pavan-firmware/EH-Master-Repo/docs/phase12-production-blockers.md

# EH Home — Phase 12 Production Blockers & Readiness Matrix

**Date**: 2026-08-30
**Baseline Commit**: `342425b`
**Feature Branch**: `feature/phase12-production-readiness`

---

## 1. Blocker Classification Matrix

| Item / Issue | Severity | Classification | Status | Rationale |
| :--- | :--- | :--- | :--- | :--- |
| **Physical ESP32 Bench Testing** | HIGH | **BLOCKER** | 🟡 **PENDING HARDWARE ATTACHMENT** | Hardware test harness (`test_esp32_lifecycle.py`) requires a physically attached ESP32 over serial/USB to certify physical relay actuation, BLE advertising, and Wi-Fi throughput. |
| **Host Software & Cloud Services**| N/A | **PASS** | ✅ **COMPLETE** | 23/23 monorepo test suites passing, 28/28 database tables verified, EMQX 5.8 mTLS verified. |
| **Flutter Mobile Application** | N/A | **PASS** | ✅ **COMPLETE** | 115/115 tests passing, `dart analyze` reports 0 issues, formatting clean. |
| **Security & Secret Leakage** | N/A | **PASS** | ✅ **COMPLETE** | Zero tracked secrets, private keys, or passwords across entire repository. |
| **Environment Separation** | N/A | **PASS** | ✅ **COMPLETE** | DEV, STAGING, and PRODUCTION environment configuration schemas separated and validated. |

---

## 2. Production Decision

- **HOST / CLOUD / APP READINESS**: **PASS (100% READY)**
- **PHYSICAL PRODUCTION RELEASE GATE**: **BLOCKED BY PHYSICAL HARDWARE ACCEPTANCE**
