pavan-firmware/EH-Master-Repo/docs/phase12-production-readiness.md

# EH Home — Phase 12: Production Readiness & End-to-End Acceptance

> **STATUS**: GATED — HOST & SUITES 100% PASS (23/23) | PHYSICAL HARDWARE VALIDATION PENDING ATTACHED ESP32
> **BASELINE**: `origin/main` (`342425b`)
> **BRANCH**: `feature/phase12-production-readiness`

---

## 1. Production Readiness Verification Matrix

| Area | Status | Evidence / Notes |
| :--- | :--- | :--- |
| **Monorepo Test Suites** | ✅ PASS (23/23) | `node scripts/validate-repo.js` passes all 23 suites across firmware, manufacturing, backend, contracts, and Flutter. |
| **SQL Migrations Lifecycle** | ✅ PASS (28/28) | All 28 managed relational tables verified symmetric UP/DOWN (`verify-migrations.js`). |
| **Real EMQX 5.8 mTLS** | ✅ PASS (22/22) | Full mTLS connection on port 8883, certificate verification, and ACL enforcement verified (`test_real_emqx.js`). |
| **Auth & Multi-Tenancy** | ✅ PASS (25/25) | RS256 JWT validation, refresh token rotation, cross-home access rejection (`phase7a-auth.test.js`). |
| **Realtime SSE & Workers** | ✅ PASS (20/20) | SSE event streaming, timeout worker, outbox backoff worker, and stale detection (`phase7b-realtime.test.js`). |
| **Automation & Schedules** | ✅ PASS (6/6) | Scene execution, automation conditions/actions, cron scheduling worker (`phase10-automation.test.js`). |
| **Device Mgmt & Health** | ✅ PASS (7/7) | Unified health, renaming, room movement, zero secret leakage (`phase11-device-management.test.js`). |
| **Environment Configuration** | ✅ PASS (6/6) | Dev, staging, and production environment schemas verified; zero tracked secrets (`validate-environment.js`). |
| **Flutter App & Tests** | ✅ PASS (115/115) | Dart formatting, Flutter analyzer (0 issues), and full Flutter test suite passed. |
| **Physical ESP32 Validation** | 🟡 PENDING | Host logic verified; physical hardware lifecycle marked PENDING until physical ESP32 attached. |

---

## 2. Security & Secret Boundary Enforcement

1. **Zero Secret Commits**:
   - Automated scan confirmed no private keys, JWT secrets, database passwords, or device root certificates are stored in source code.
2. **Factory Identity Immutability**:
   - `fact_v2` NVS partition holds immutable device UUID, hardware revision, serial number, and factory certificates.
   - Remote user unclaim / removal only modifies `device_authorizations` and never clears factory flash.
3. **Safe Transport & Encryption**:
   - Public internet traffic is secured over HTTPS / TLS.
   - Device cloud communication is enforced over mTLS Port 8883 against EMQX broker with strict deviceId CN matching.
   - BLE commissioning utilizes AES-GCM EH-PROV/1 transcript handshake.

---

## 3. Physical Validation Checklist & Blocker Classification

| Test ID | Subsystem | Physical Gate Description | Status | Classification |
| :--- | :--- | :--- | :--- | :--- |
| **HW-01** | BLE GATT | Discover proprietary EH-PROV/1 UUID and read characteristic `6105` | PENDING | REQUIRED FOR PROD RELEASE |
| **HW-02** | Provisioning | 4-step AES-GCM EH-PROV/1 handshake & Wi-Fi credential transfer | PENDING | REQUIRED FOR PROD RELEASE |
| **HW-03** | Cloud mTLS | ESP32 establishes mTLS on port 8883 to EMQX broker | PENDING | REQUIRED FOR PROD RELEASE |
| **HW-04** | Relay Actuation | Cloud command triggers physical relay with sub-50ms latency | PENDING | REQUIRED FOR PROD RELEASE |
| **HW-05** | Physical Override | Physical wall toggle overrides cloud state with ISR event | PENDING | REQUIRED FOR PROD RELEASE |
| **HW-06** | Telemetry Ingestion| BL0942 energy monitoring UART1 reporting V/I/P/E to backend | PENDING | REQUIRED FOR PROD RELEASE |
| **HW-07** | Power Cycle | Device recovers from abrupt power-cut without losing identity | PENDING | REQUIRED FOR PROD RELEASE |
| **HW-08** | Signed OTA | Partition swap and bootloader rollback verification | PENDING | REQUIRED FOR PROD RELEASE |

---

## 4. Production Release Gate Statement

The software, backend infrastructure, cloud database schemas, mobile application UI/logic, and firmware host simulation layers meet 100% of production readiness criteria. Full production certification requires physical execution of the attached hardware test harness upon connecting the target ESP32 switch unit.
