pavan-firmware/EH-Master-Repo/docs/planning/phase-1.md

# Phase 1 Summary: Canonical Contracts & Foundation Freeze

Phase 1 establishes the canonical contracts, metadata schemas, modular backend skeleton, database migrations, and verification test suites according to Architecture Specification v3.2.

## Artifacts Created
1. `packages/contracts/` - Canonical JSON Schemas & TypeScript interfaces (18 schemas).
2. `packages/contracts/validator.js` - Lightweight Schema validator engine.
3. `packages/contracts/tests/contract-test.js` - Automated schema validation test suite.
4. `product-definitions/smart-switch/3x/` - Metadata and asset mappings for EH Smart Switch 3X.
5. `packages/contracts/capability/capability-registry.json` - Registered capabilities (14 capabilities).
6. `backend/migrations/001_initial_schema.sql` - PostgreSQL migration script.
7. `tools/device-simulator/` - Contract-compliant hardware simulation engine.
8. `docker-compose.yml` - Foundation development services.
9. `smart_home_application_v1` - Preserved existing Flutter application.
