pavan-firmware/EH-Master-Repo/firmware/platforms/esp32/smart-switch-app/main/app_lifecycle.c

#include "app_lifecycle.h"
#include <stdio.h>
#include <string.h>

#ifdef ESP_PLATFORM
#include "esp_log.h"
#define TAG "APP_LIFECYCLE"
#else
#define TAG "APP_LIFECYCLE"
#define ESP_LOGI(tag, fmt, ...) printf("[%s] " fmt "\n", tag, ##__VA_ARGS__)
#define ESP_LOGW(tag, fmt, ...) printf("[WARN:%s] " fmt "\n", tag, ##__VA_ARGS__)
#define ESP_LOGE(tag, fmt, ...) printf("[ERR:%s] " fmt "\n", tag, ##__VA_ARGS__)
#endif

#define MAX_LISTENERS 4

static app_lifecycle_state_t s_current_state = APP_STATE_FACTORY_NEW;
static bool s_commissioned = false;
static app_lifecycle_listener_t s_listeners[MAX_LISTENERS];
static size_t s_listener_count = 0;

static const char* s_state_names[] = {
    "FACTORY_NEW",
    "BLE_COMMISSIONING",
    "WIFI_CONNECTING",
    "LOCAL_OPERATIONAL",
    "MQTT_CONNECTING",
    "ACTIVE",
    "ERROR_RECOVERY",
    "OTA_UPDATING"
};

void app_lifecycle_init(void)
{
    s_current_state = APP_STATE_FACTORY_NEW;
    s_commissioned = false;
    s_listener_count = 0;
    memset(s_listeners, 0, sizeof(s_listeners));
    ESP_LOGI(TAG, "Lifecycle initialized to %s", s_state_names[s_current_state]);
}

app_lifecycle_state_t app_lifecycle_get_state(void)
{
    return s_current_state;
}

const char* app_lifecycle_get_state_name(app_lifecycle_state_t state)
{
    if ((size_t)state < sizeof(s_state_names)/sizeof(s_state_names[0])) {
        return s_state_names[state];
    }
    return "UNKNOWN";
}

bool app_lifecycle_set_state(app_lifecycle_state_t new_state)
{
    if (s_current_state == new_state) {
        return true;
    }

    // Valid transition checks
    bool valid = false;
    switch (s_current_state) {
        case APP_STATE_FACTORY_NEW:
            valid = (new_state == APP_STATE_BLE_COMMISSIONING || new_state == APP_STATE_WIFI_CONNECTING);
            break;
        case APP_STATE_BLE_COMMISSIONING:
            valid = (new_state == APP_STATE_WIFI_CONNECTING || new_state == APP_STATE_ERROR_RECOVERY || new_state == APP_STATE_FACTORY_NEW);
            break;
        case APP_STATE_WIFI_CONNECTING:
            valid = (new_state == APP_STATE_LOCAL_OPERATIONAL || new_state == APP_STATE_MQTT_CONNECTING || new_state == APP_STATE_ERROR_RECOVERY || new_state == APP_STATE_BLE_COMMISSIONING);
            break;
        case APP_STATE_LOCAL_OPERATIONAL:
            valid = (new_state == APP_STATE_MQTT_CONNECTING || new_state == APP_STATE_ACTIVE || new_state == APP_STATE_ERROR_RECOVERY || new_state == APP_STATE_WIFI_CONNECTING || new_state == APP_STATE_OTA_UPDATING || new_state == APP_STATE_FACTORY_NEW);
            break;
        case APP_STATE_MQTT_CONNECTING:
            valid = (new_state == APP_STATE_ACTIVE || new_state == APP_STATE_LOCAL_OPERATIONAL || new_state == APP_STATE_ERROR_RECOVERY || new_state == APP_STATE_WIFI_CONNECTING || new_state == APP_STATE_OTA_UPDATING);
            break;
        case APP_STATE_ACTIVE:
            valid = (new_state == APP_STATE_LOCAL_OPERATIONAL || new_state == APP_STATE_ERROR_RECOVERY || new_state == APP_STATE_WIFI_CONNECTING || new_state == APP_STATE_OTA_UPDATING || new_state == APP_STATE_FACTORY_NEW);
            break;
        case APP_STATE_ERROR_RECOVERY:
            valid = (new_state == APP_STATE_LOCAL_OPERATIONAL || new_state == APP_STATE_MQTT_CONNECTING || new_state == APP_STATE_ACTIVE || new_state == APP_STATE_WIFI_CONNECTING || new_state == APP_STATE_BLE_COMMISSIONING || new_state == APP_STATE_FACTORY_NEW);
            break;
        case APP_STATE_OTA_UPDATING:
            valid = (new_state == APP_STATE_ACTIVE || new_state == APP_STATE_LOCAL_OPERATIONAL || new_state == APP_STATE_ERROR_RECOVERY);
            break;
        default:
            valid = false;
            break;
    }

    if (!valid) {
        ESP_LOGW(TAG, "Invalid state transition rejected: %s -> %s",
                 app_lifecycle_get_state_name(s_current_state),
                 app_lifecycle_get_state_name(new_state));
        return false;
    }

    app_lifecycle_state_t old_state = s_current_state;
    s_current_state = new_state;
    ESP_LOGI(TAG, "State transition: %s -> %s",
             app_lifecycle_get_state_name(old_state),
             app_lifecycle_get_state_name(new_state));

    for (size_t i = 0; i < s_listener_count; i++) {
        if (s_listeners[i]) {
            s_listeners[i](old_state, new_state);
        }
    }
    return true;
}

void app_lifecycle_register_listener(app_lifecycle_listener_t listener)
{
    if (listener && s_listener_count < MAX_LISTENERS) {
        s_listeners[s_listener_count++] = listener;
    }
}

bool app_lifecycle_is_secret_accessible(void)
{
    // Secret is accessible ONLY when uncommissioned and in initial setup states
    return (!s_commissioned) && (s_current_state == APP_STATE_FACTORY_NEW || s_current_state == APP_STATE_BLE_COMMISSIONING);
}

void app_lifecycle_mark_commissioned(void)
{
    s_commissioned = true;
    ESP_LOGI(TAG, "Device marked commissioned. Secret access locked.");
}
