pavan-firmware/EH-Master-Repo/firmware/platforms/esp32/smart-switch-app/main/relay_manager.h

#ifndef EH_RELAY_MANAGER_H
#define EH_RELAY_MANAGER_H

#include <stdbool.h>
#include <stdint.h>

#ifdef ESP_PLATFORM
#include "sdkconfig.h"
#endif

#ifdef __cplusplus
extern "C" {
#endif

#define EH_RELAY_CHANNEL_COUNT 3

// Relay Module Trigger Logic:
// Standard optocoupler 5V relay modules are Active LOW (0 = Relay ON, 1 = Relay OFF)
#define EH_RELAY_ACTIVE_LEVEL 0
#define EH_RELAY_POWER_TO_LEVEL(pwr) ((pwr) ? EH_RELAY_ACTIVE_LEVEL : (!EH_RELAY_ACTIVE_LEVEL))

// Target-Specific Hardware Pin Mapping
#if defined(CONFIG_IDF_TARGET_ESP32)
// ESP32-D0WD Development Board Profile: GPIO 18, 19, 21
#define GPIO_RELAY_CH1 18
#define GPIO_RELAY_CH2 19
#define GPIO_RELAY_CH3 21
#elif defined(CONFIG_IDF_TARGET_ESP32C6)
// ESP32-C6 Production Profile: GPIO 18, 19, 20
#define GPIO_RELAY_CH1 18
#define GPIO_RELAY_CH2 19
#define GPIO_RELAY_CH3 20
#elif defined(CONFIG_IDF_TARGET_ESP32C3)
// ESP32-C3 Production Profile: GPIO 18, 19, 10 (GPIO 10 avoids UART0 RX collision on GPIO 20)
#define GPIO_RELAY_CH1 18
#define GPIO_RELAY_CH2 19
#define GPIO_RELAY_CH3 10
#elif !defined(ESP_PLATFORM)
// Host simulation fallback
#define GPIO_RELAY_CH1 18
#define GPIO_RELAY_CH2 19
#define GPIO_RELAY_CH3 20
#else
#error "Unsupported EH Home MCU target in relay_manager.h"
#endif

typedef void (*relay_state_change_cb_t)(uint8_t channel_index, bool new_power, const char* source);

/**
 * Initialize relay GPIOs as outputs and restore last persisted NVS states (or default to OFF).
 */
void relay_manager_init(void);

/**
 * Clear persisted relay states from NVS (for factory reset).
 */
void relay_manager_clear_persisted_states(void);

/**
 * Set power for a specific channel (1-indexed: 1..3).
 * Returns true if channel is valid and state applied.
 */
bool relay_manager_set_power(uint8_t channel_index, bool power, const char* source);

/**
 * Toggle power for a specific channel.
 */
bool relay_manager_toggle_power(uint8_t channel_index, const char* source);

/**
 * Get current power state for a channel (1..3).
 */
bool relay_manager_get_power(uint8_t channel_index);

/**
 * Register callback to receive notification on state changes.
 */
void relay_manager_register_change_cb(relay_state_change_cb_t cb);

#ifdef __cplusplus
}
#endif

#endif /* EH_RELAY_MANAGER_H */
