pavan-firmware/EH-Master-Repo/firmware/platforms/esp32/smart-switch-app/main/ota_manager.h

#ifndef EH_OTA_MANAGER_H
#define EH_OTA_MANAGER_H

#include <stdbool.h>
#include <stdint.h>
#include <stddef.h>

#ifdef __cplusplus
extern "C" {
#endif

#define EH_OTA_MAX_BIN_SIZE_BYTES (1792 * 1024) /* 1.75MB partition bound */

typedef enum {
    EH_OTA_STATE_IDLE = 0,
    EH_OTA_STATE_DOWNLOADING,
    EH_OTA_STATE_VERIFYING,
    EH_OTA_STATE_INSTALLING,
    EH_OTA_STATE_REBOOTING,
    EH_OTA_STATE_ROLLED_BACK,
    EH_OTA_STATE_FAILED
} eh_ota_state_t;

typedef struct {
    uint8_t schema_version;
    char release_id[37];
    char product_variant_id[32];
    char hardware_revision[16];
    char version[32];
    char min_version[32];
    size_t binary_size_bytes;
    char sha256[65];
    char ed25519_signature[129];
    char download_url[256];
} eh_ota_manifest_t;

/**
 * Initialize OTA subsystem and check if running image is awaiting confirmation.
 */
void ota_manager_init(void);

/**
 * Get current OTA progress state.
 */
eh_ota_state_t ota_manager_get_state(void);

/**
 * Compare semver strings (returns >0 if v1 > v2, 0 if v1==v2, <0 if v1 < v2).
 */
int ota_semver_compare(const char* v1, const char* v2);

/**
 * Validate manifest against running version for anti-rollback and signature integrity.
 * Returns true if update is permitted.
 */
bool ota_validate_manifest(const eh_ota_manifest_t* manifest, const char* current_version);

/**
 * Confirm boot validity to prevent automatic bootloader rollback.
 * Call only after successful Wi-Fi + MQTT connection.
 */
void ota_manager_confirm_boot_valid(void);

/**
 * Start OTA update with given signed manifest over HTTPS.
 */
bool ota_manager_start_update(const eh_ota_manifest_t* manifest);

#ifdef __cplusplus
}
#endif

#endif /* EH_OTA_MANAGER_H */
